Qirab/QirabTravelDigitisationCradle/PDF/Group Images/QTCv2.2.1_0_Open.png

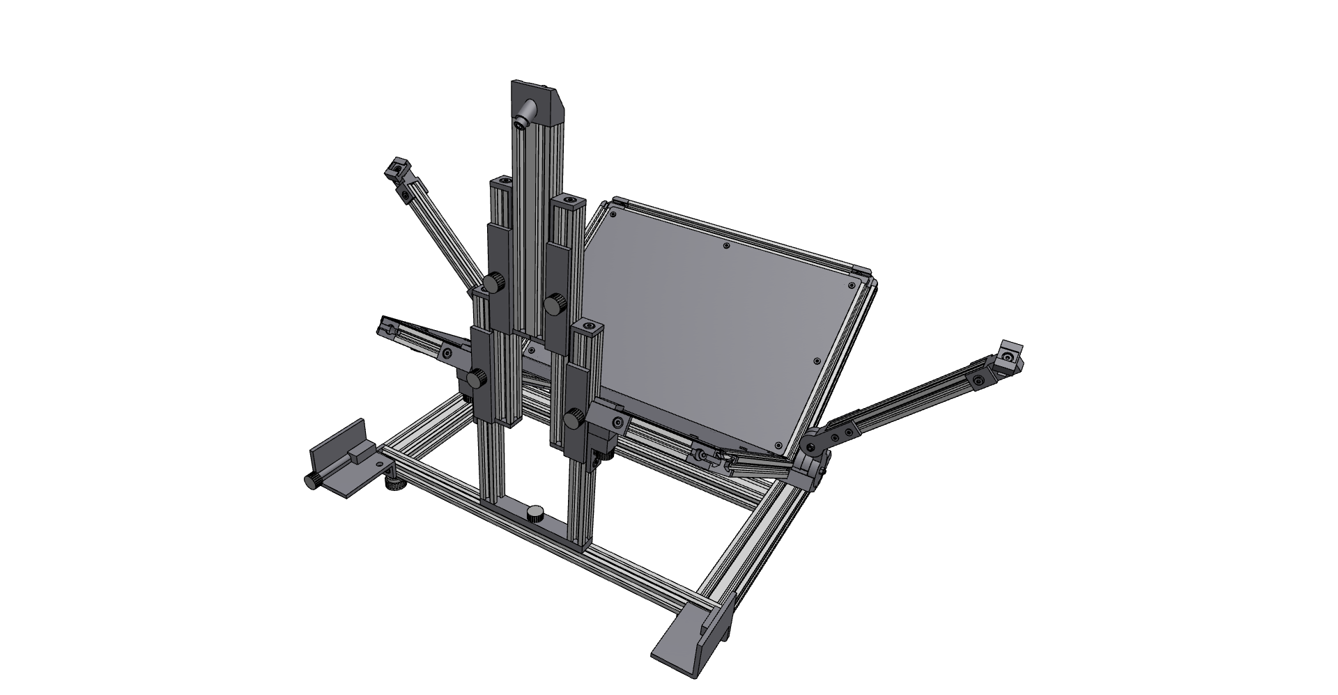
PDF/Group Images/QTCv2.2.1_0_Open.png
