Qirab/QirabTravelDigitisationCradle/3DPRINT/4 EACH/QTC Foot.3mf

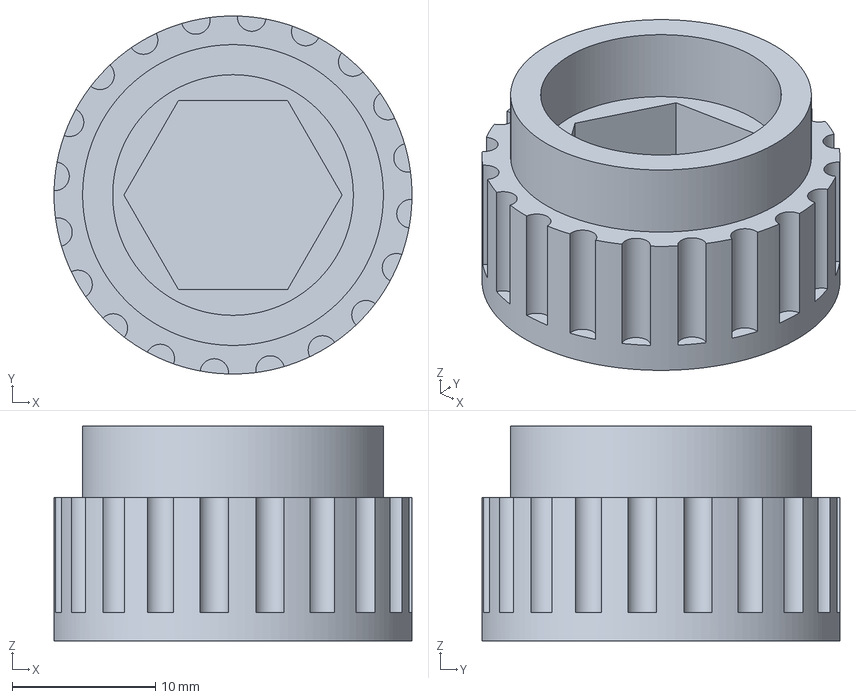
[picture p20: CAD file, 2026-09-14]
3DPRINT/4 EACH/QTC Foot.3mf
25.0 x 25.0 x 15.0 mm
