Qirab/QirabTravelDigitisationCradle/3DPRINT/4 EACH/QTC Box QTC50.3mf

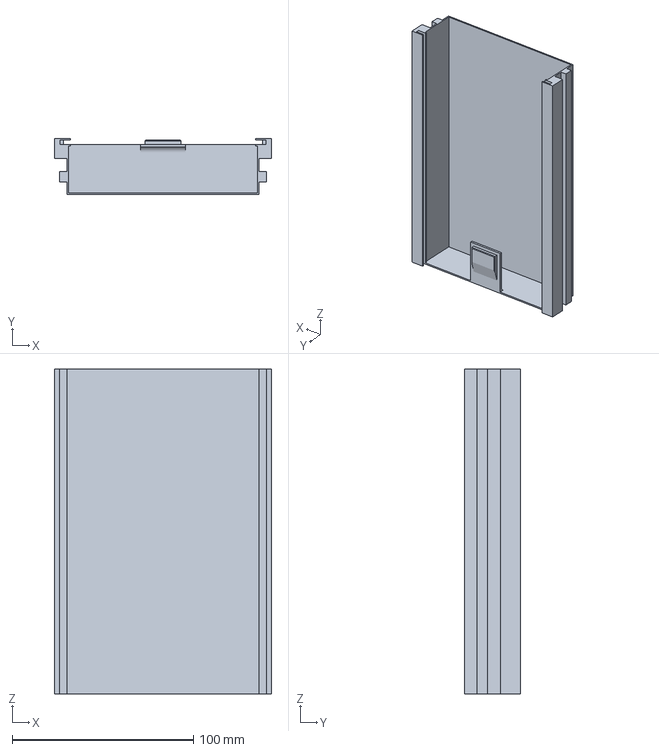
[picture p21: CAD file, 2026-09-14]
3DPRINT/4 EACH/QTC Box QTC50.3mf
120.0 x 31.0 x 179.5 mm
