Qirab/QirabTravelDigitisationCradle/3DPRINT/1 EACH/QTC 20mmNOTCH Frame Hinge Outer L.3mf

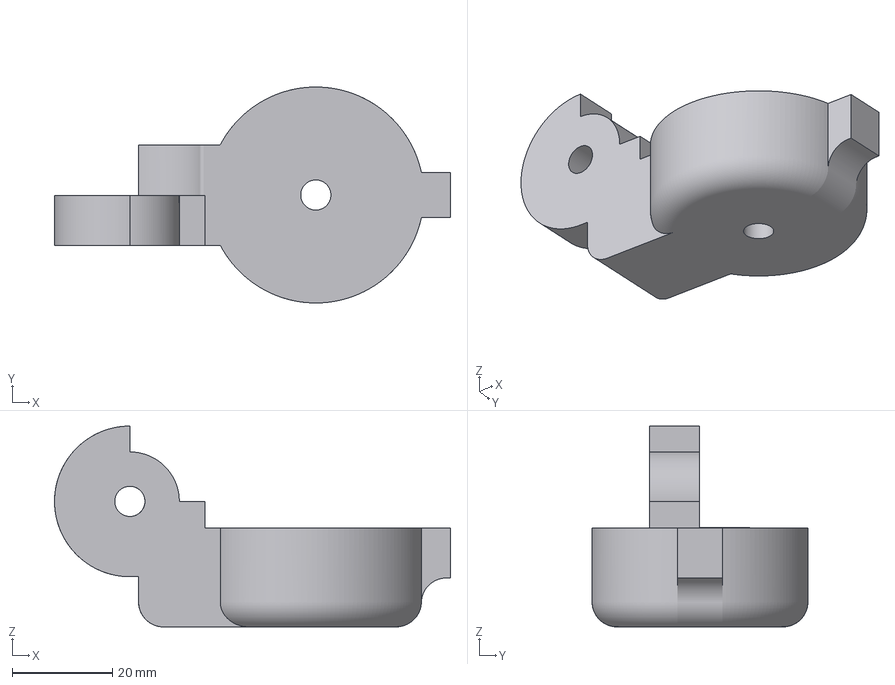
[picture p22: CAD file, 2026-10-01]
3DPRINT/1 EACH/QTC 20mmNOTCH Frame Hinge Outer L.3mf
78.8 x 43.0 x 40.0 mm
