Qirab/QirabTravelDigitisationCradle/3DPRINT/2 EACH/QTC Cold Shoe v3.3mf

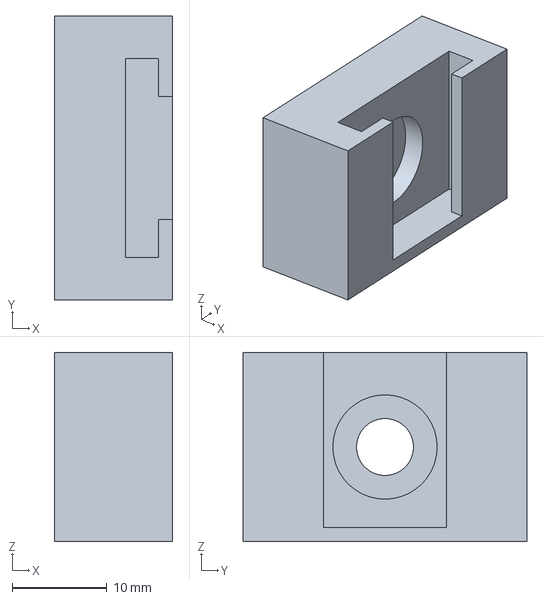
[picture p23: CAD file, 2026-09-14]
3DPRINT/2 EACH/QTC Cold Shoe v3.3mf
12.5 x 30.0 x 20.0 mm
