Qirab/QirabTravelDigitisationCradle/3DPRINT/2 EACH/QTC Box Small Lid QTC50.3mf

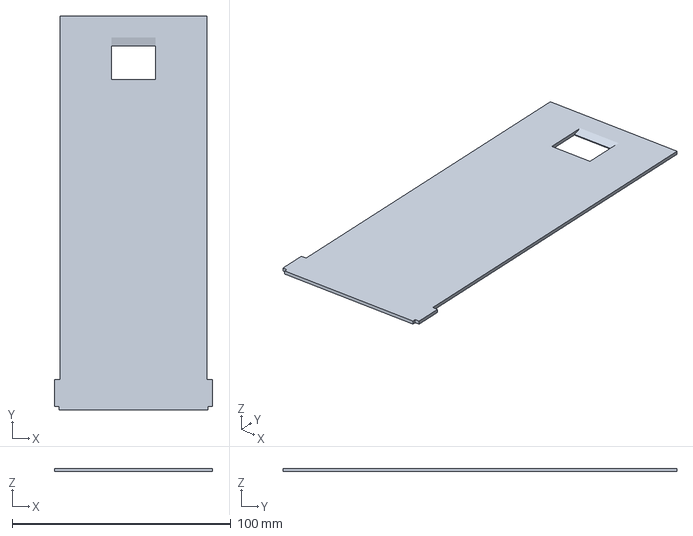
[picture p24: CAD file, 2026-09-14]
3DPRINT/2 EACH/QTC Box Small Lid QTC50.3mf
72.2 x 180.0 x 1.50 mm
