Qirab/QirabTravelDigitisationCradle/3DPRINT/2 EACH/QTC Box Small Cup.3mf

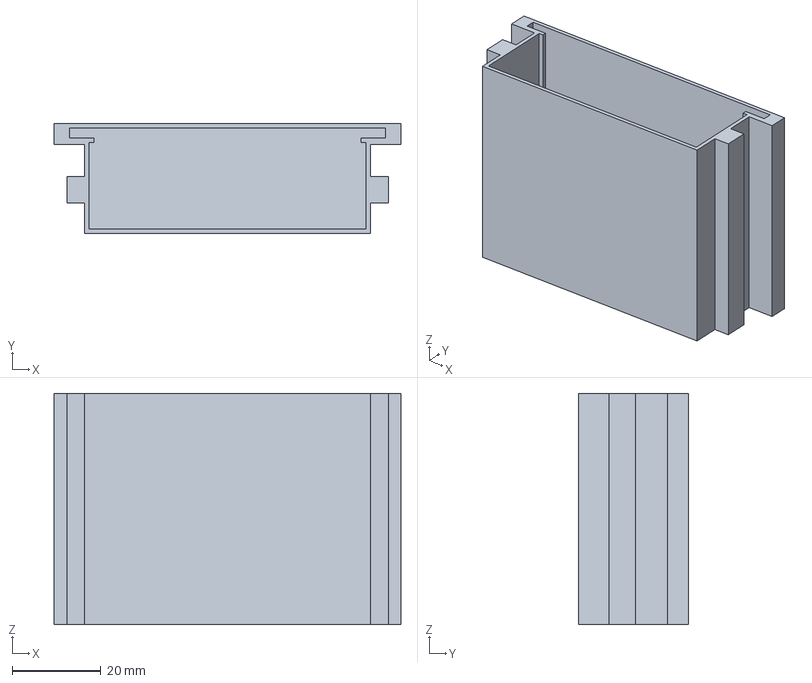
[picture p25: CAD file, 2026-09-14]
3DPRINT/2 EACH/QTC Box Small Cup.3mf
78.0 x 24.8 x 52.0 mm
