Qirab/QirabTravelDigitisationCradle/3DPRINT/2 EACH/QTC Camera Arm Spacer.3mf

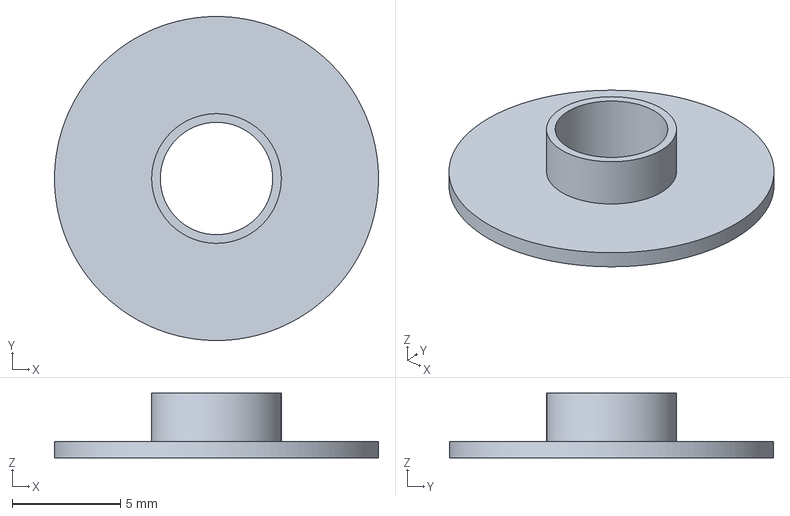
[picture p26: CAD file, 2026-09-14]
3DPRINT/2 EACH/QTC Camera Arm Spacer.3mf
15.0 x 15.0 x 3.00 mm
