Qirab/QirabTravelDigitisationCradle/3DPRINT/1 EACH/QTC Light Arm Hinge LEFT EXPERIMENTAL.3mf

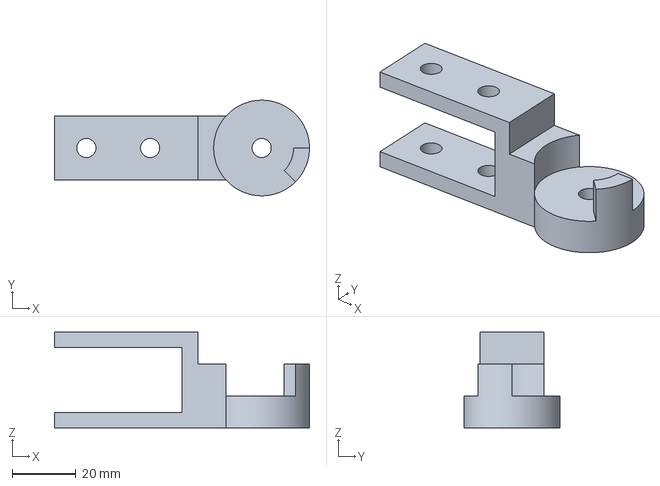
[picture p27: CAD file, 2026-09-14]
3DPRINT/1 EACH/QTC Light Arm Hinge LEFT EXPERIMENTAL.3mf
80.0 x 30.0 x 30.0 mm
