Qirab/QirabTravelDigitisationCradle/3DPRINT/2 EACH/QTC CamArm Slider.3mf

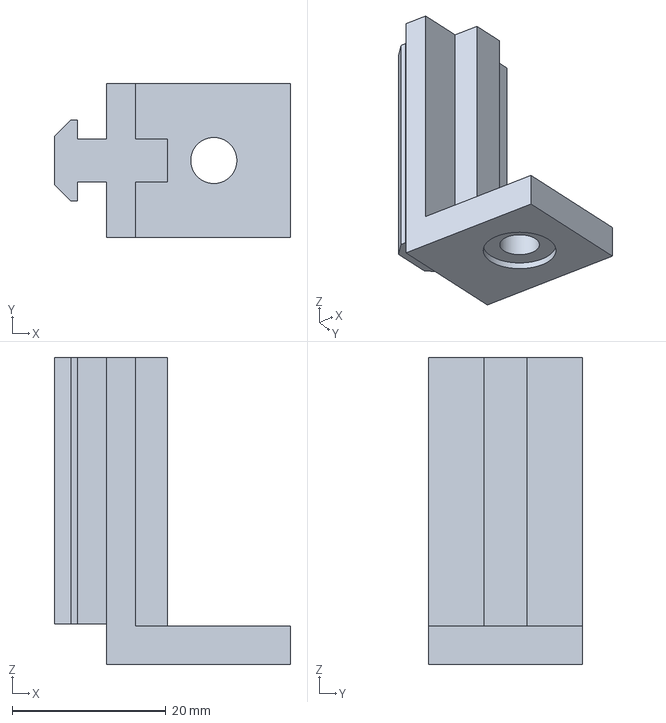
[picture p28: CAD file, 2026-09-14]
3DPRINT/2 EACH/QTC CamArm Slider.3mf
30.8 x 20.0 x 40.0 mm
