Qirab/QirabTravelDigitisationCradle/3DPRINT/1 EACH/QTC Support Board.3mf

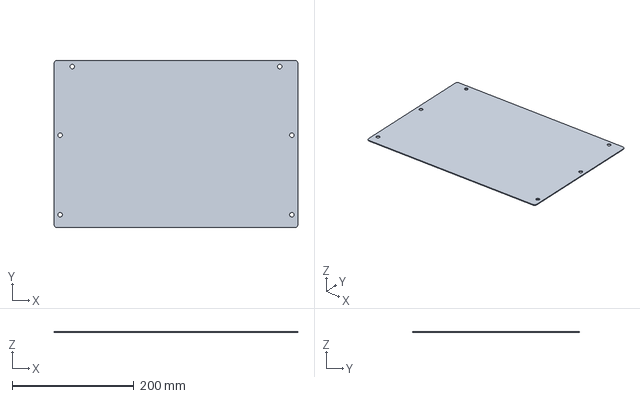
[picture p29: CAD file, 2026-09-14]
3DPRINT/1 EACH/QTC Support Board.3mf
400.0 x 274.0 x 1.50 mm
