Qirab/QirabTravelDigitisationCradle/3DPRINT/2 EACH/QTC CamArm Upper Lock Plug.3mf

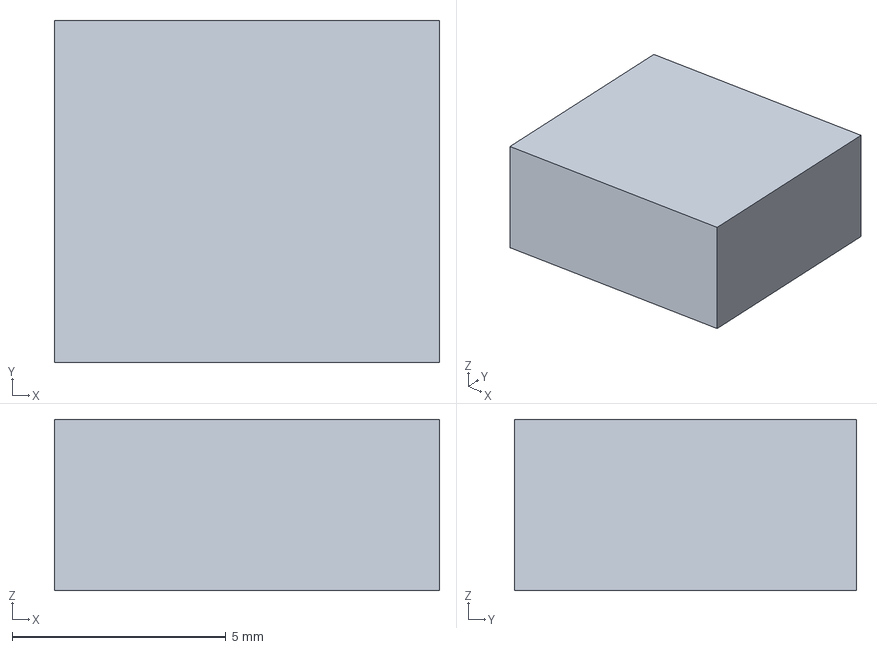
[picture p30: CAD file, 2026-09-14]
3DPRINT/2 EACH/QTC CamArm Upper Lock Plug.3mf
9.00 x 8.00 x 4.00 mm
