Qirab/QirabTravelDigitisationCradle/3DPRINT/1 EACH/QTC Light Arm Top LEFT.3mf

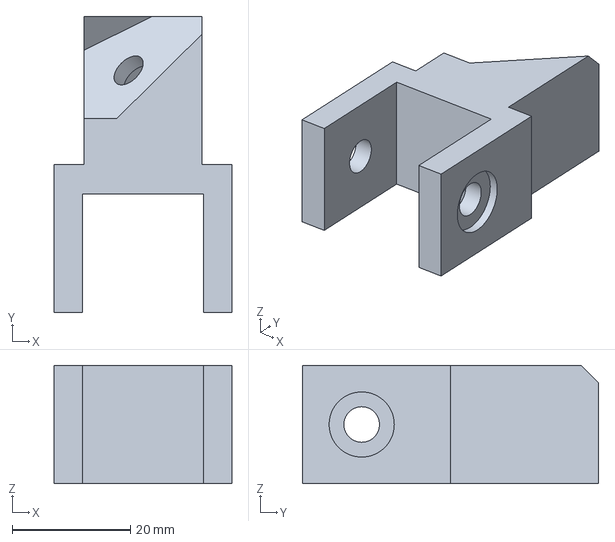
[picture p31: CAD file, 2026-09-14]
3DPRINT/1 EACH/QTC Light Arm Top LEFT.3mf
30.0 x 50.0 x 20.0 mm
