Qirab/QirabTravelDigitisationCradle/3DPRINT/2 EACH/Frame Hinge Outer R (21).3mf

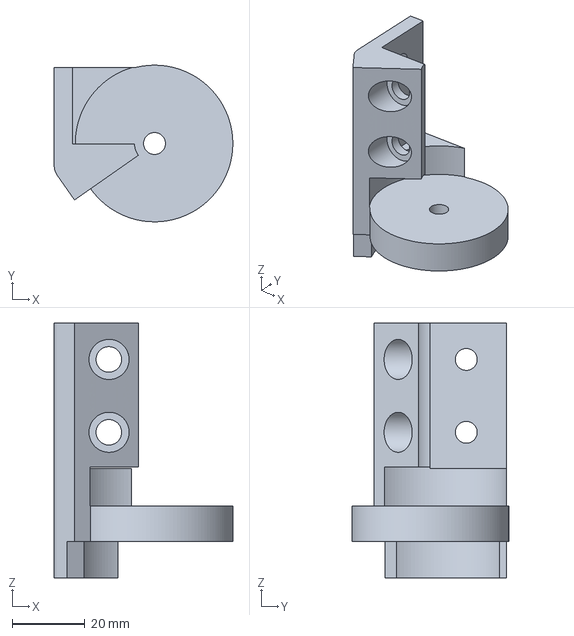
[picture p32: CAD file, 2025-09-22]
3DPRINT/2 EACH/Frame Hinge Outer R (21).3mf
49.0 x 43.0 x 70.0 mm
