Qirab/QirabTravelDigitisationCradle/3DPRINT/1 EACH/QTC Frame Hinge Outer LEFT.3mf

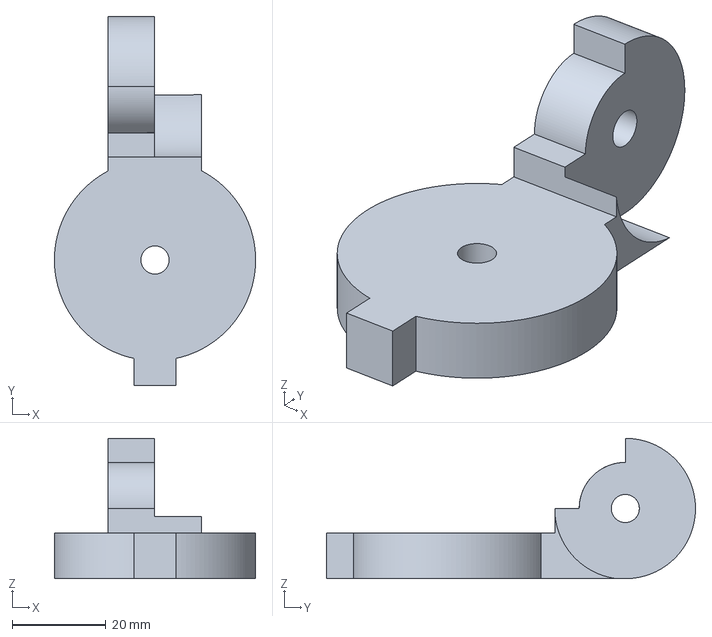
[picture p33: CAD file, 2026-09-14]
3DPRINT/1 EACH/QTC Frame Hinge Outer LEFT.3mf
43.0 x 78.8 x 30.0 mm
