Qirab/QirabTravelDigitisationCradle/3DPRINT/2 EACH/R arm top (8).3mf

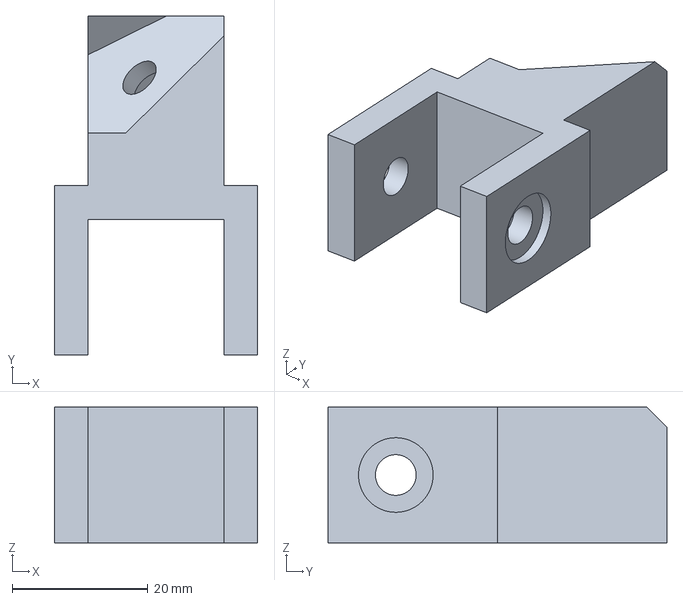
[picture p34: CAD file, 2025-09-22]
3DPRINT/2 EACH/R arm top (8).3mf
30.0 x 50.0 x 20.0 mm
