Qirab/QirabTravelDigitisationCradle/3DPRINT/1 EACH/QTC CamArm Upper Lock L.3mf

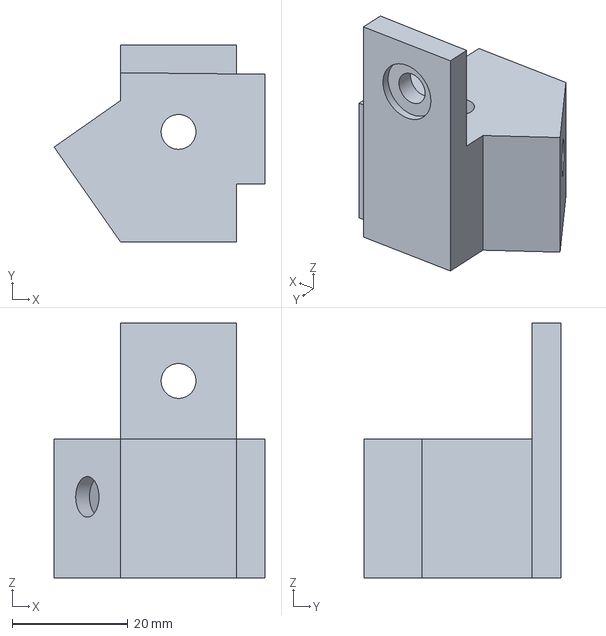
[picture p35: CAD file, 2026-09-14]
3DPRINT/1 EACH/QTC CamArm Upper Lock L.3mf
36.4 x 34.0 x 44.0 mm
