Qirab/QirabTravelDigitisationCradle/3DPRINT/1 EACH/QTC CamArm Base.3mf

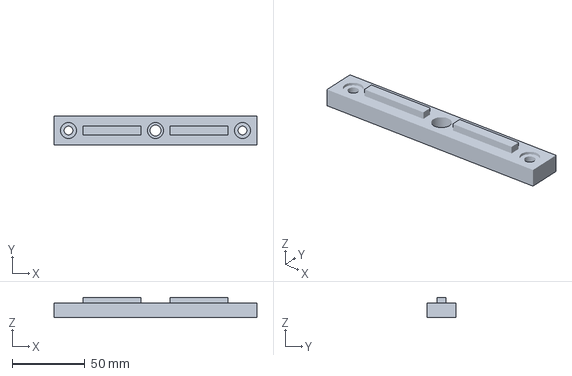
[picture p36: CAD file, 2026-09-14]
3DPRINT/1 EACH/QTC CamArm Base.3mf
140.0 x 20.0 x 14.0 mm
