Qirab/QirabTravelDigitisationCradle/3DPRINT/1 EACH/QTC Camera Arm Retaining Ring.3mf

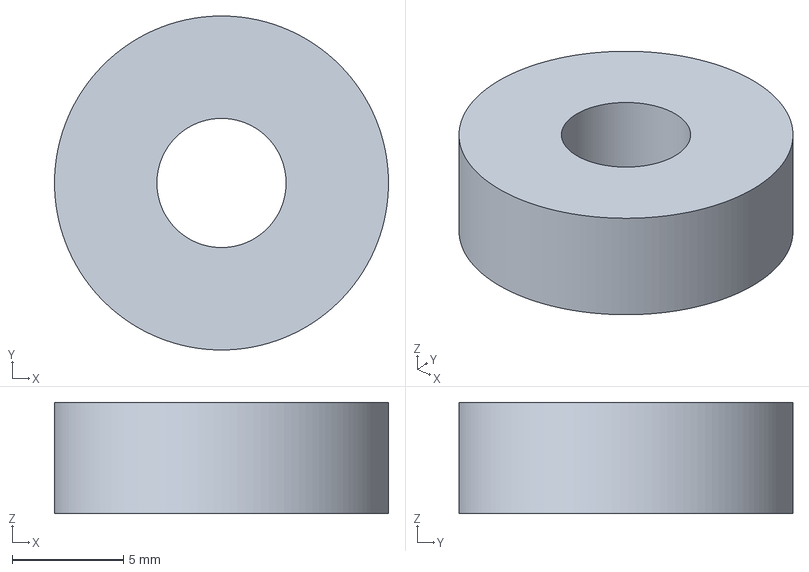
[picture p37: CAD file, 2026-09-14]
3DPRINT/1 EACH/QTC Camera Arm Retaining Ring.3mf
15.0 x 15.0 x 5.00 mm
