Qirab/QirabTravelDigitisationCradle/3DPRINT/1 EACH/QTC Lock End Block L.3mf

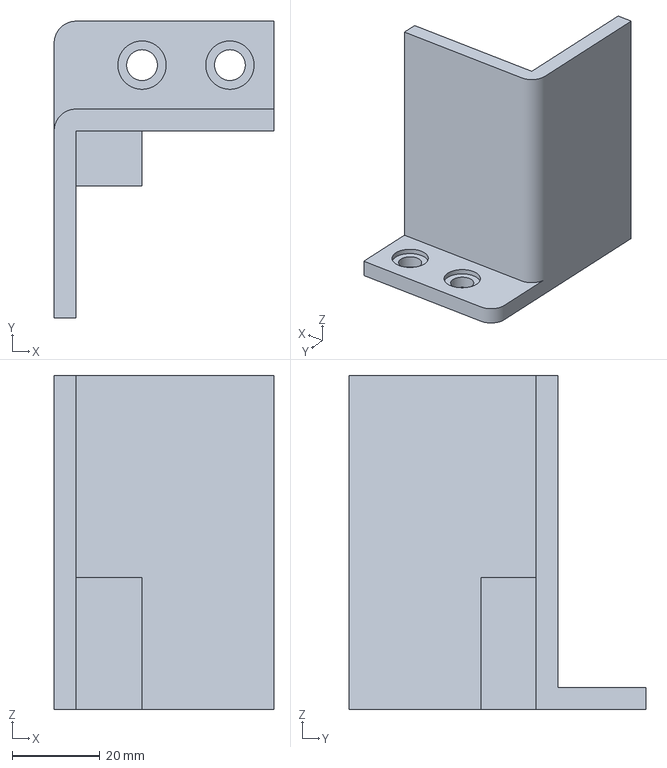
[picture p38: CAD file, 2026-09-14]
3DPRINT/1 EACH/QTC Lock End Block L.3mf
50.0 x 67.5 x 76.0 mm
