Qirab/QirabTravelDigitisationCradle/3DPRINT/1 EACH/QTC Lock End Block R.3mf

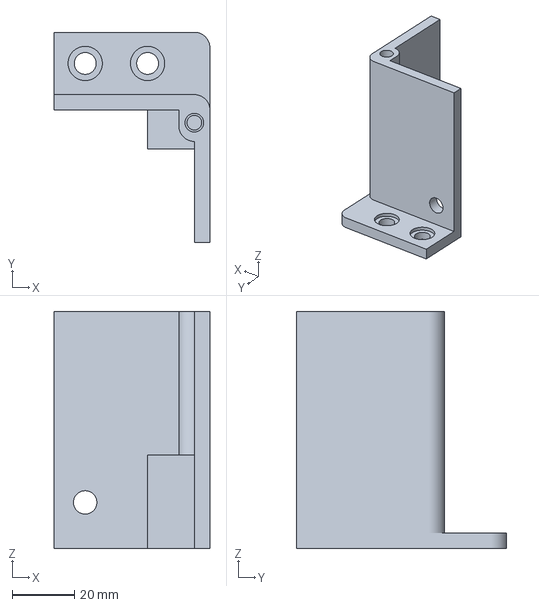
[picture p39: CAD file, 2026-09-14]
3DPRINT/1 EACH/QTC Lock End Block R.3mf
50.0 x 67.5 x 76.0 mm
