Qirab/QirabTravelDigitisationCradle/3DPRINT/1 EACH/QTC Cam Block.3mf

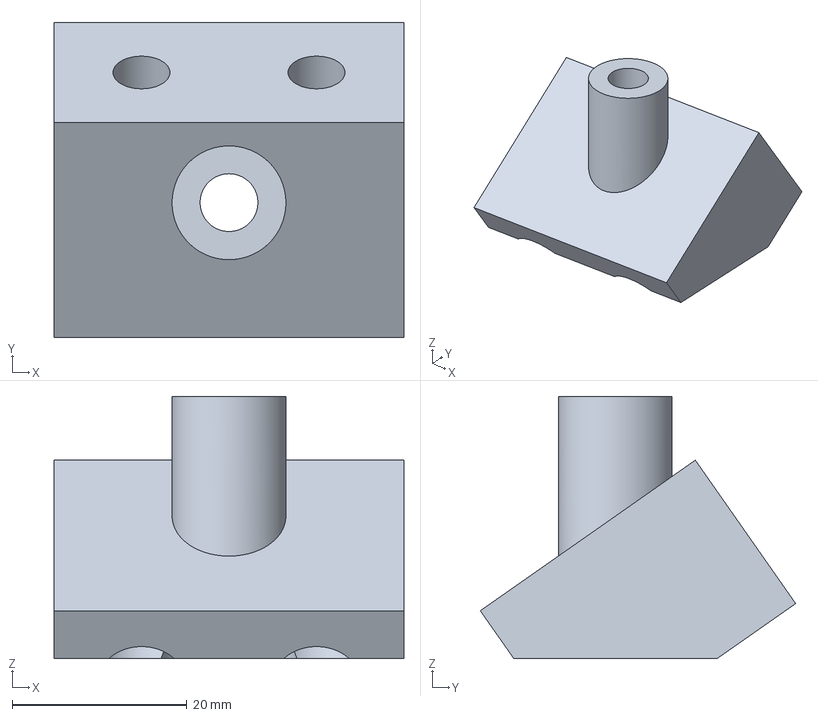
[picture p40: CAD file, 2026-09-14]
3DPRINT/1 EACH/QTC Cam Block.3mf
40.0 x 36.0 x 30.0 mm
